gridballast/gridballastOpenHardware/Hardware/Controller/Info/Simulations/CT/CT Bias Only.asc

I1: current; SINE(0 {AMP/TURNS} 60)
R1: res; 33
R2: res; 10k
R3: res; 10k
V1: voltage; 3.3
Named nets: out, 0, 3.3V, CT_A, CT_B
Ratio: CT Detection 40A ==> 20mA, since it is a 1:2000 turn
.tran 0 40ms 0 0.001ms
Configured for 80A through CT, which translates to 40mA across R1.
.param AMP=80
This paramerer specifies the current passed throug the current transformer
.step param AMP 0 100 1
.param TURNS=2000
