gridballast/gridballastOpenHardware/Hardware/Controller/Info/Simulations/CT/CT Clamping.asc

C1: cap; 100µ
I1: current; SINE(0 .04 60)
R1: res; 33
R2: res; 1k
R3: res; 1k
R4: res; 10k
R5: res; 10k
R6: res; 10k
U1: UniversalOpamp2
V1: voltage; 3.3
Named nets: 0, 3.3V, out, CT
CT Detection 40A ==> 20mA
.tran 0 200ms 0 .001s
